DCC-EX/EX-T3-WiFi/src/DCCExCS.h

#ifndef DCC_EX_CS_H
#define DCC_EX_CS_H

#include <Arduino.h>
#include <bitset>
#include <regex>
#include <Events.h>
#include <AsyncTCP.h>

class DCCExCS : public Events {
  private:
    AsyncClient& _csClient;
    TimerHandle_t _timeout;

    struct {
      const char* match;
      std::function<void (std::smatch &matches)> matched;
    } _response;
    
    void createTimeout();
    void deleteTimeout();
  public:
    struct Event {
      static constexpr uint8_t TIMEOUT = 0;
      static constexpr uint8_t VERSION = 1;
      static constexpr uint8_t BROADCAST_LOCO = 2;
      static constexpr uint8_t BROADCAST_POWER = 3;
      static constexpr uint8_t PROGRAM_READ = 4;
      static constexpr uint8_t PROGRAM_WRITE = 5;
    };

    struct Version {
      String version;
      String board;
      String shield;
      String build;

      Version() { }
      Version(String& version, String& board, String& shield, String& build)
        : version(version), board(board), shield(shield), build(build) { }
      Version(const char* version, const char* board, const char* shield, const char* build)
        : version(version), board(board), shield(shield), build(build) { }
    };

    struct Power {
      enum : uint8_t {
        ALL,
        MAIN,
        PROG,
        JOIN
      };

      bool main = false;
      bool prog = false;
      bool join = false;

      Power() { }
      Power(const Power& power) : main(power.main), prog(power.prog), join(power.join) { }
    };

    struct Loco {
      uint16_t address;
      uint8_t speed;
      uint8_t direction;
      std::bitset<32> functions;
      Loco(uint16_t address)
          : address(address), speed(UINT8_MAX), direction(UINT8_MAX), functions(0) { }
      Loco(uint16_t address, uint8_t speed, bool direction, uint32_t functions)
          : address(address), speed(speed), direction(direction), functions(functions) { }
      Loco(uint16_t address, uint8_t speedCode, uint32_t functions)
          : address(address), speed(max(0, (speedCode & 0x7F) - 1)),
            direction((speedCode & 0x80) == 128), functions(functions) { }
      Loco(const Loco& loco) : address(loco.address), speed(loco.speed), direction(loco.direction), functions(loco.functions) { }
    };

    DCCExCS(AsyncClient& csClient);

    void handleCS(uint8_t* data, uint16_t size);
    
    void getCSVersion();

    void getCSPower();
    void setCSPower(uint8_t power, bool state);

    void emergencyStopAll();
    void acquireLoco(uint16_t address);
    void releaseLoco(uint16_t address);
    void setLocoThrottle(uint16_t address, int8_t speed, uint8_t direction);
    void setLocoFn(uint16_t address, uint8_t fn, bool state);

    void getLocoAddress();
    void setLocoAddress(uint16_t address);
    void getLocoCVByte(uint16_t cv);
    void setLocoCVByte(uint16_t cv, uint8_t value);
    void getLocoCVBit(uint16_t cv, uint8_t bit);
    void setLocoCVBit(uint16_t cv, uint8_t bit, bool value);

    void accessory(uint16_t address, bool state);

    void setAckLimit(uint16_t limit);
    void setAckMin(uint16_t min);
    void setAckMax(uint16_t max);
};

#endif
