DCC-EX/EX-T3-WiFi/myFilter.cpp

#include "Arduino.h"
#include "CommandDistributor.h"

/*
 * Adds extra command to your Command Station which can be used by the throttle
 */

void myFilter(Print *stream, byte &opcode, byte &paramCount, int16_t p[]) {
  (void)stream; // Stops warning
  if (opcode == 'U') {
    if (paramCount == 1 && p[0] == 'P') {
      CommandDistributor::broadcastPower();
    }
    opcode = '\0';
  }
};
