DCC-EX/EX-T3-WiFi/src/SettingsUI.h

#ifndef SETTINGS_UI_H
#define SETTINGS_UI_H

#include <UI.h>
#include <Settings.h>

class SettingsUI : public UI {
  private:
    class Page {
      protected:
        SettingsUI& _ui;
      public:
        Page(SettingsUI& ui) : _ui(ui) { }

        virtual void show() = 0;
    };

    class Page1 : Page {
      using Page::Page;

      char _speedStepLabels[3][2] = { "1", "2", "4" };
      char _swipActionLabels[7][12] = { "None", "Keypad", "Loco Names", "Loco Groups", "Next Loco", "Prev Loco", "Release" };

      void swipeAction(void* button, uint8_t& gesture, uint8_t actions);
    public:
      void show();
    } Page1;

    class Page2 : Page {
      using Page::Page;

      char _rotationLabels[3][30] = { "Standard", "Inverted", "Accelerometer (if applicable)" };
      char _pinLabels[2][8] = { "Not Set", "Pin Set" };
    public:
      void show();
    } Page2;

    std::vector<std::function<void (void)>> _pages = {
      [this] { Page1.show(); },
      [this] { Page2.show(); }
    };
  public:
    SettingsUI();
    ~SettingsUI();
};

#endif
